eziocangialosi/OVL-IoT/unit-tests/mqtt-gprs-sim800l.ino

// Select your modem:
#define TINY_GSM_MODEM_SIM800
// #define TINY_GSM_MODEM_SIM808
// #define TINY_GSM_MODEM_SIM868
// #define TINY_GSM_MODEM_SIM900
// #define TINY_GSM_MODEM_SIM7000
// #define TINY_GSM_MODEM_SIM7000SSL
// #define TINY_GSM_MODEM_SIM7080
// #define TINY_GSM_MODEM_SIM5360
// #define TINY_GSM_MODEM_SIM7600
// #define TINY_GSM_MODEM_UBLOX
// #define TINY_GSM_MODEM_SARAR4
// #define TINY_GSM_MODEM_M95
// #define TINY_GSM_MODEM_BG96
// #define TINY_GSM_MODEM_A6
// #define TINY_GSM_MODEM_A7
// #define TINY_GSM_MODEM_M590
// #define TINY_GSM_MODEM_MC60
// #define TINY_GSM_MODEM_MC60E
// #define TINY_GSM_MODEM_ESP8266
// #define TINY_GSM_MODEM_XBEE
// #define TINY_GSM_MODEM_SEQUANS_MONARCH

// set GSM PIN, if any
#define GSM_PIN ""

// Your GPRS credentials, if any
const char apn[]      = "example.com";
const char gprsUser[] = "";
const char gprsPass[] = "";

// MQTT details
#define MQTT_PORT 1883

const char* broker = "example.com";

const char* topicLed       = "unit-test/led";
const char* topicDebug     = "unit-test/debug";

#include <TinyGsmClient.h>
#include <PubSubClient.h>

TinyGsm        modem(Serial1);
TinyGsmClient client(modem);
PubSubClient  mqtt(client);

#define LED_PIN 2
int ledStatus = LOW;

uint32_t lastReconnectAttempt = 0;

void mqttCallback(char* topic, byte* payload, unsigned int len) {
  Serial.print("Message arrived [");
  Serial.print(topic);
  Serial.print("]: ");
  Serial.write(payload, len);
  Serial.println();

  String msg = "";
  for(unsigned int i = 0; i < len; i++){
    msg += (char)payload[i];
  }

  // Only proceed if incoming message's topic matches
  if (String(topic) == topicLed) {
      if((msg == "HIGH" && ledStatus == LOW) || (msg == "LOW" && ledStatus == HIGH)){
          ledStatus = !ledStatus;
          digitalWrite(LED_PIN, ledStatus);
          mqtt.publish(topicDebug, ledStatus ? "1" : "0");
      }
  }
}

boolean mqttConnect() {
  Serial.print("Connecting to ");
  Serial.print(broker);

  // Connect to MQTT Broker
  boolean status = mqtt.connect("GsmClientTest");

  if (status == false) {
    Serial.println(" fail");
    return false;
  }
  Serial.println(" success");
  mqtt.publish(topicDebug, "Unit test mqtt via GPRS started");
  mqtt.subscribe(topicLed);
  return mqtt.connected();
}


void setup() {
  // Set console baud rate
  Serial.begin(115200);
  delay(10);

  pinMode(LED_PIN, OUTPUT);

  Serial.println("Wait...");

  // Set GSM module baud rate
  Serial1.begin(9600);
  delay(6000);

  Serial.println("Initializing modem...");
  modem.restart();

  String modemInfo = modem.getModemInfo();
  Serial.print("Modem Info: ");
  Serial.println(modemInfo);
  // Unlock your SIM card with a PIN if needed
  if (GSM_PIN && modem.getSimStatus() != 3) { modem.simUnlock(GSM_PIN); }

  Serial.print("Waiting for network...");
  if (!modem.waitForNetwork()) {
    Serial.println(" fail");
    delay(10000);
    return;
  }
  Serial.println(" success");

  if (modem.isNetworkConnected()) { Serial.println("Network connected"); }

  // GPRS connection parameters are usually set after network registration
  Serial.print(F("Connecting to "));
  Serial.print(apn);
  if (!modem.gprsConnect(apn, gprsUser, gprsPass)) {
    Serial.println(" fail");
    delay(10000);
    return;
  }
  Serial.println(" success");

  if (modem.isGprsConnected()) { Serial.println("GPRS connected"); }

  // MQTT Broker setup
  mqtt.setServer(broker, MQTT_PORT);
  mqtt.setCallback(mqttCallback);
}

void loop() {
  // Make sure we're still registered on the network
  if (!modem.isNetworkConnected()) {
    Serial.println("Network disconnected");
    if (!modem.waitForNetwork(180000L, true)) {
      Serial.println(" fail");
      delay(10000);
      return;
    }
    if (modem.isNetworkConnected()) {
      Serial.println("Network re-connected");
    }

    // and make sure GPRS/EPS is still connected
    if (!modem.isGprsConnected()) {
      Serial.println("GPRS disconnected!");
      Serial.print(F("Connecting to "));
      Serial.print(apn);
      if (!modem.gprsConnect(apn, gprsUser, gprsPass)) {
        Serial.println(" fail");
        delay(10000);
        return;
      }
      if (modem.isGprsConnected()) { Serial.println("GPRS reconnected"); }
    }
  }

  if (!mqtt.connected()) {
    Serial.println("=== MQTT NOT CONNECTED ===");
    // Reconnect every 10 seconds
    uint32_t t = millis();
    if (t - lastReconnectAttempt > 10000L) {
      lastReconnectAttempt = t;
      if (mqttConnect()) { lastReconnectAttempt = 0; }
    }
    delay(100);
    return;
  }

  mqtt.loop();
}
