eziocangialosi/OVL-IoT/unit-tests/gprs-sim800l-TinyGSM.ino

// Select your modem:
#define TINY_GSM_MODEM_SIM800
// #define TINY_GSM_MODEM_SIM808
// #define TINY_GSM_MODEM_SIM868
// #define TINY_GSM_MODEM_SIM900
// #define TINY_GSM_MODEM_SIM7000
// #define TINY_GSM_MODEM_SIM7000SSL
// #define TINY_GSM_MODEM_SIM7080
// #define TINY_GSM_MODEM_SIM5360
// #define TINY_GSM_MODEM_SIM7600
// #define TINY_GSM_MODEM_UBLOX
// #define TINY_GSM_MODEM_SARAR4
// #define TINY_GSM_MODEM_M95
// #define TINY_GSM_MODEM_BG96
// #define TINY_GSM_MODEM_A6
// #define TINY_GSM_MODEM_A7
// #define TINY_GSM_MODEM_M590
// #define TINY_GSM_MODEM_MC60
// #define TINY_GSM_MODEM_MC60E
// #define TINY_GSM_MODEM_ESP8266
// #define TINY_GSM_MODEM_XBEE
// #define TINY_GSM_MODEM_SEQUANS_MONARCH

// Set serial for debug console
#define SerialMon Serial

// Set serial for AT commands (to the module)
// Use Hardware Serial on Mega, Leonardo, Micro
#define SerialAT Serial1

// set GSM PIN, if any
#define GSM_PIN ""

// Your GPRS credentials, if any
const char apn[]      = "example.com";
const char gprsUser[] = "";
const char gprsPass[] = "";

// Server details
const char resource[]   = "/";
const char server[]   = "google.com";

#include <TinyGsmClient.h>

TinyGsm        modem(SerialAT);

TinyGsmClient  client(modem);
const int      port = 80;

void setup() {
  // Set console baud rate
  SerialMon.begin(115200);
  delay(10);

  SerialMon.println("Wait...");

  // Set GSM module baud rate
  SerialAT.begin(9600);
  delay(6000);

  // Restart takes quite some time
  // To skip it, call init() instead of restart()
  SerialMon.println("Initializing modem...");
  modem.restart();
  // modem.init();

  String modemInfo = modem.getModemInfo();
  SerialMon.print("Modem Info: ");
  SerialMon.println(modemInfo);

  if (GSM_PIN && modem.getSimStatus() != 3) { modem.simUnlock(GSM_PIN); }
}

void loop() {

  SerialMon.print("Waiting for network...");
  if (!modem.waitForNetwork()) {
    SerialMon.println(" fail");
    delay(10000);
    return;
  }
  SerialMon.println(" success");

  if (modem.isNetworkConnected()) { SerialMon.println("Network connected"); }

  SerialMon.print(F("Connecting to "));
  SerialMon.print(apn);
  if (!modem.gprsConnect(apn, gprsUser, gprsPass)) {
    SerialMon.println(" fail");
    delay(10000);
    return;
  }
  SerialMon.println(" success");

  if (modem.isGprsConnected()) { SerialMon.println("GPRS connected"); }

  SerialMon.print("Connecting to ");
  SerialMon.println(server);
  if (!client.connect(server, port)) {
    SerialMon.println(" fail");
    delay(10000);
    return;
  }
  SerialMon.println(" success");

  // Shutdown

  client.stop();
  SerialMon.println(F("Server disconnected"));
  
  modem.gprsDisconnect();
  SerialMon.println(F("GPRS disconnected"));
  
  // Do nothing forevermore
  while (true) { delay(1000); }
}
